gira0/subaru-floor-mat-retainer/preview/below-detail.png

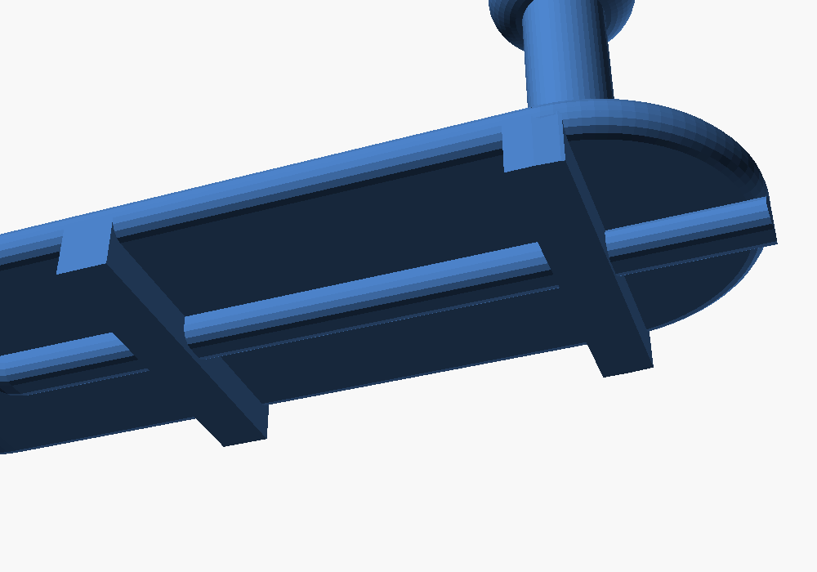
preview/below-detail.png
