gira0/subaru-floor-mat-retainer/preview/below.png

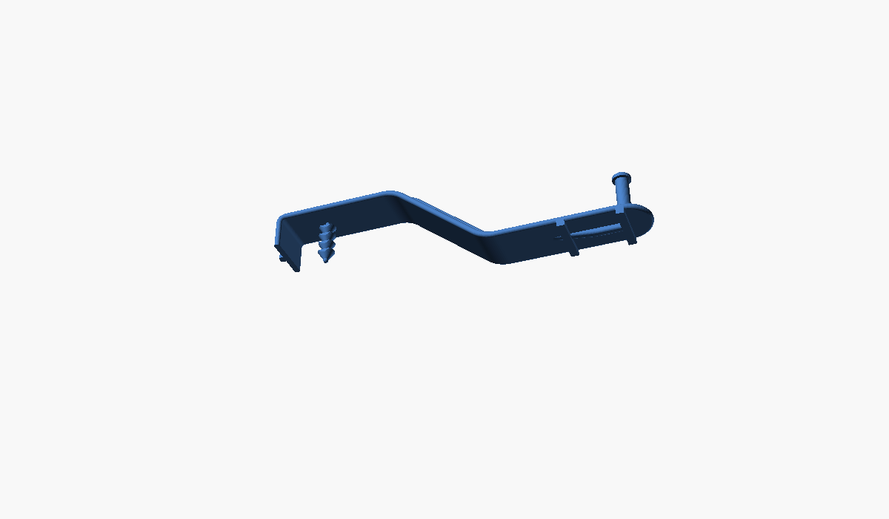
preview/below.png
