gira0/subaru-floor-mat-retainer/preview/clip-top.png

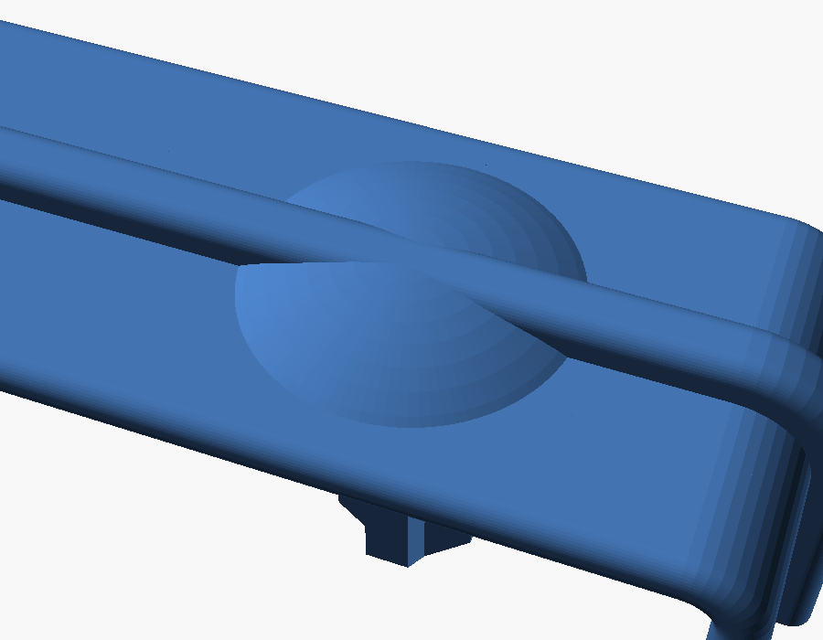
preview/clip-top.png
