gira0/subaru-floor-mat-retainer/preview/clip-varianten.png

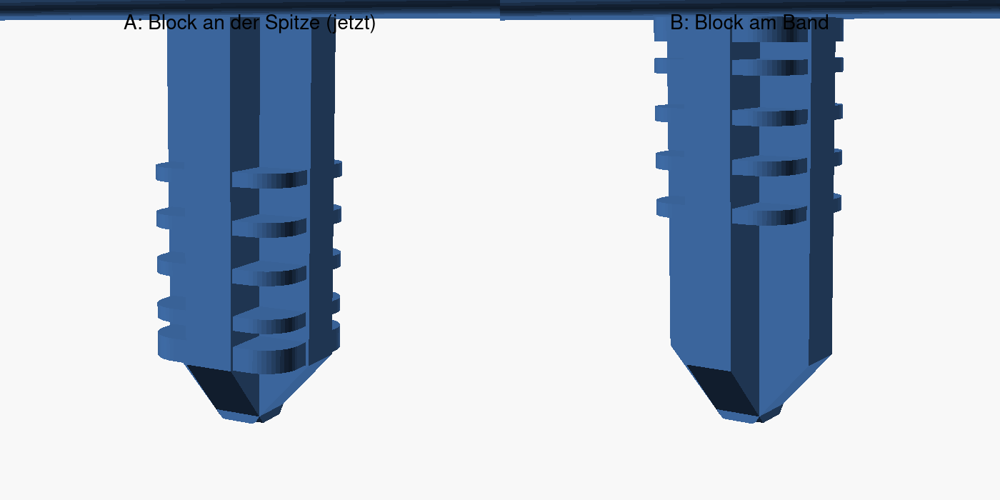
preview/clip-varianten.png
