gira0/subaru-floor-mat-retainer/preview/clip.png

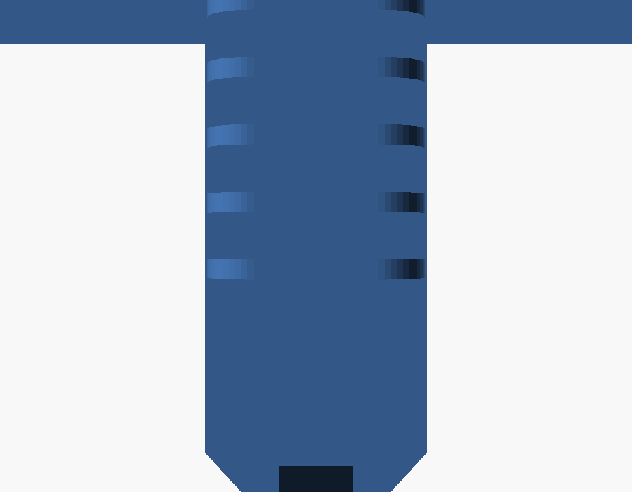
preview/clip.png
