gira0/subaru-floor-mat-retainer/preview/dimensions-check.png

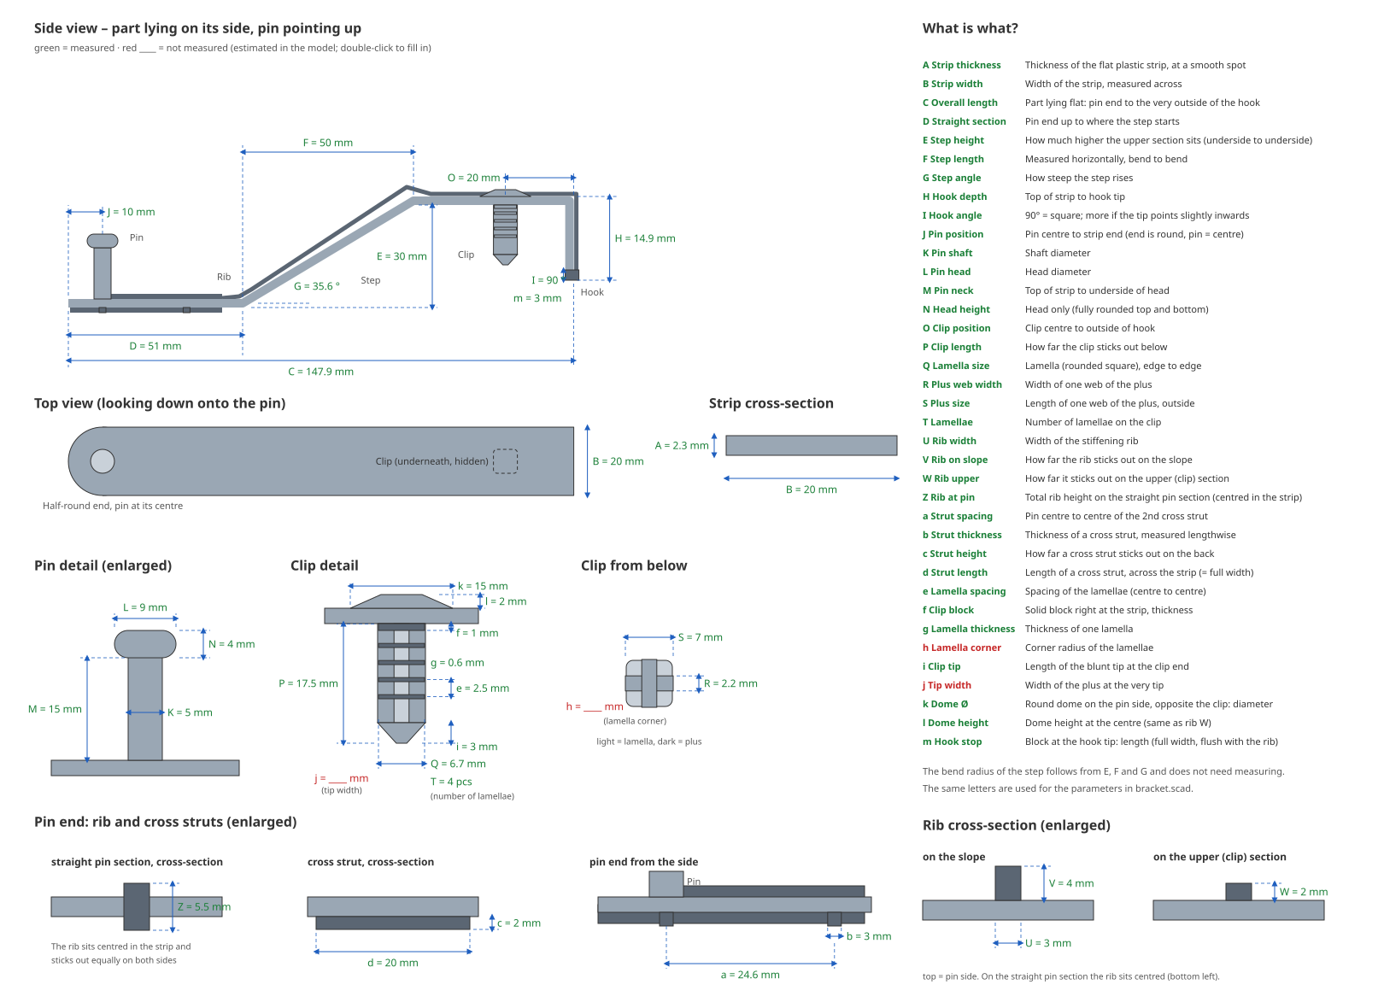
preview/dimensions-check.png
