gira0/subaru-floor-mat-retainer/preview/hook-stop2.png

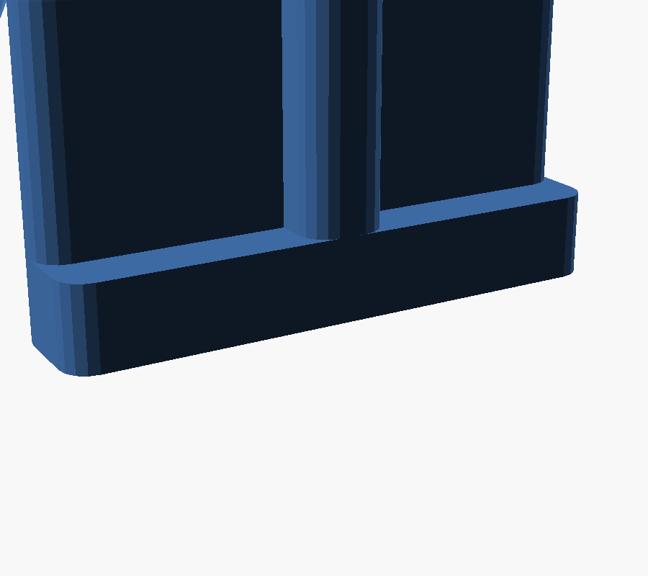
preview/hook-stop2.png
