gira0/subaru-floor-mat-retainer/preview/hook.png

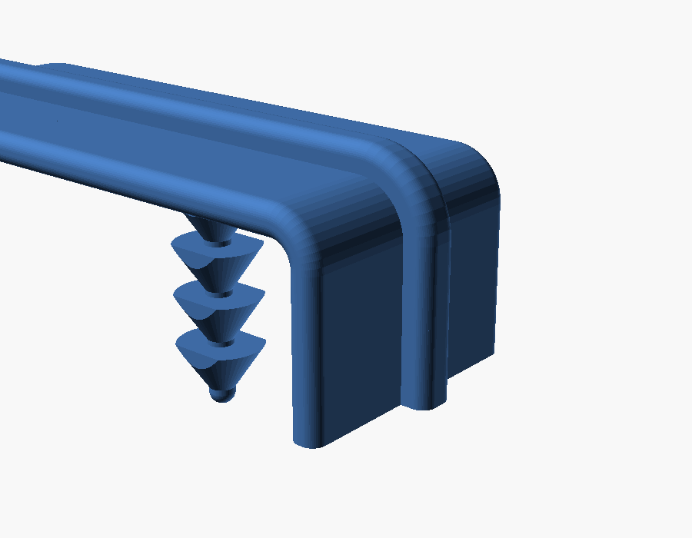
preview/hook.png
