gira0/subaru-floor-mat-retainer/preview/iso.png

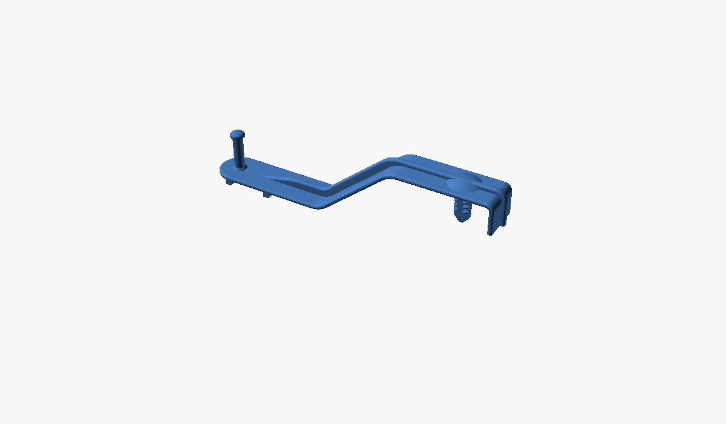
preview/iso.png
