gira0/subaru-floor-mat-retainer/preview/pin2.png

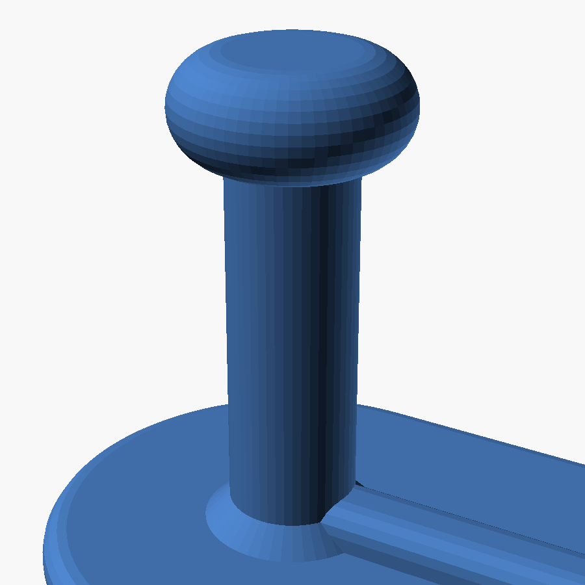
preview/pin2.png
