gira0/subaru-floor-mat-retainer/preview/pin-end-side.png

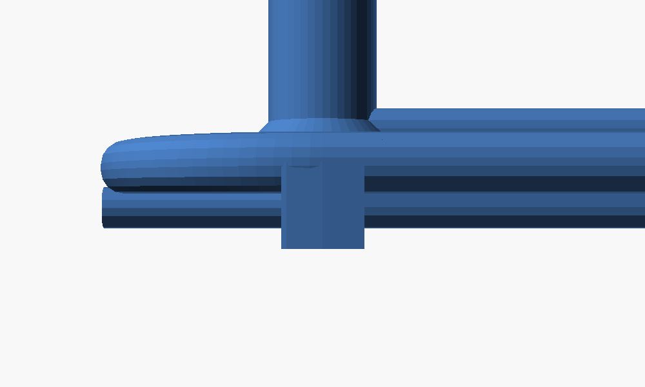
preview/pin-end-side.png
