gira0/subaru-floor-mat-retainer/preview/rib-bend1.png

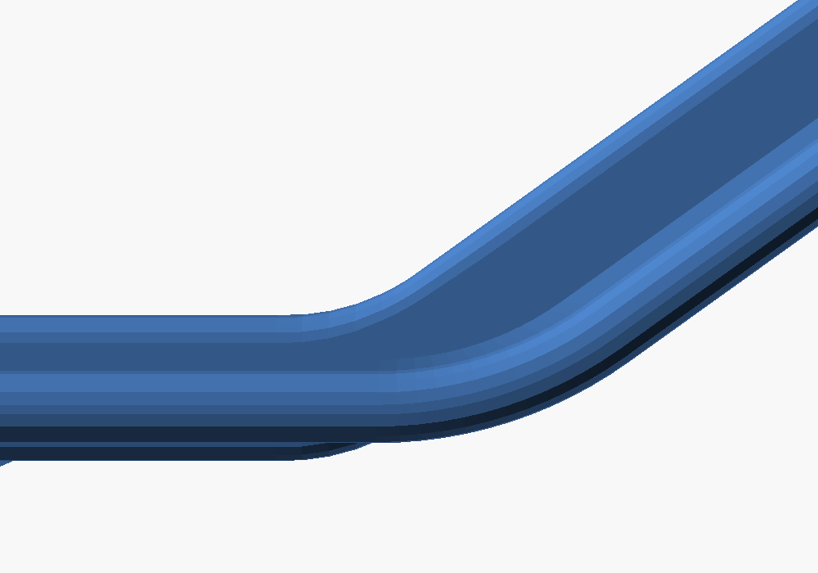
preview/rib-bend1.png
