gira0/subaru-floor-mat-retainer/preview/rib-bend1b.png

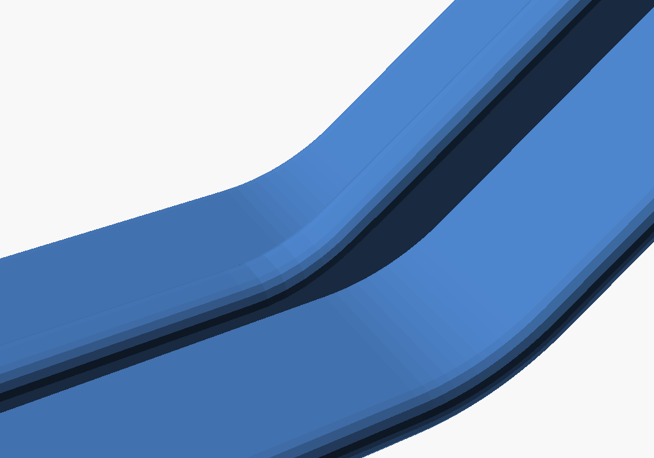
preview/rib-bend1b.png
