gira0/subaru-floor-mat-retainer/preview/rib-bend1c.png

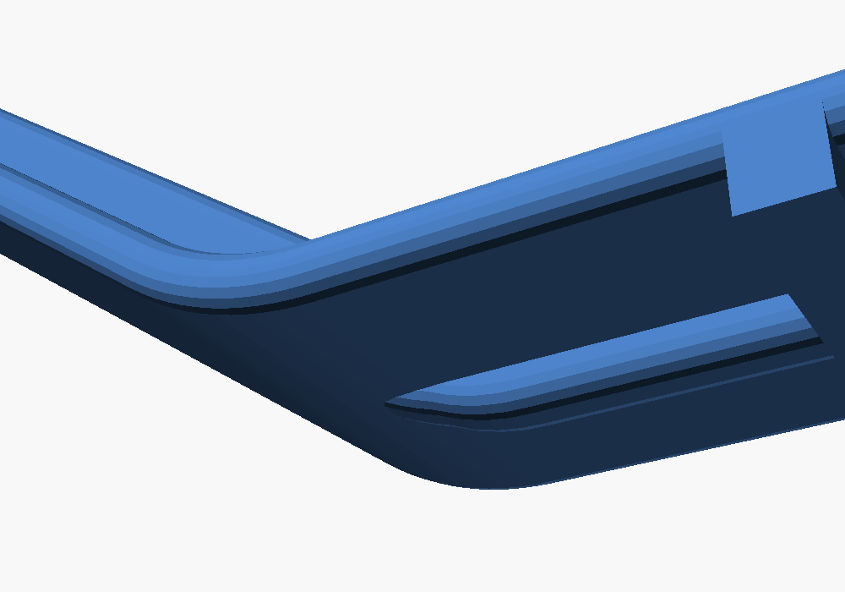
preview/rib-bend1c.png
