gira0/subaru-floor-mat-retainer/preview/rib-bend2.png

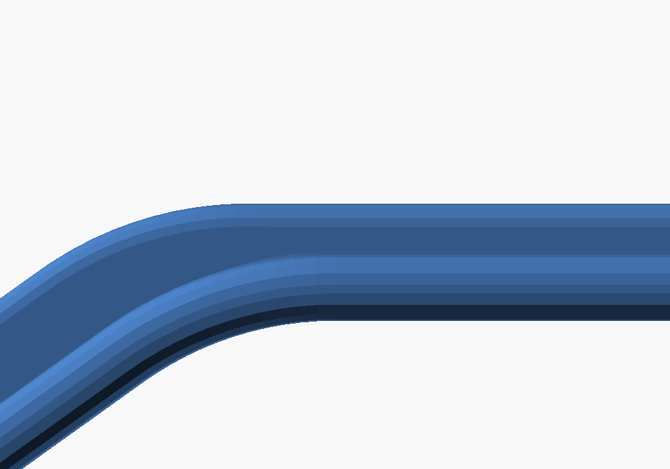
preview/rib-bend2.png
