gira0/subaru-floor-mat-retainer/preview/rib-bend2b.png

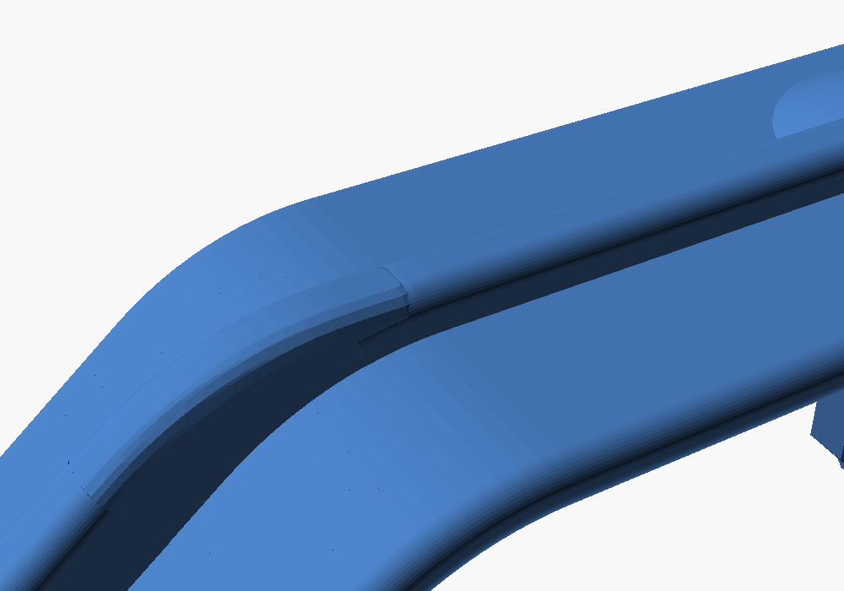
preview/rib-bend2b.png
