gira0/subaru-floor-mat-retainer/preview/rib-pin2.png

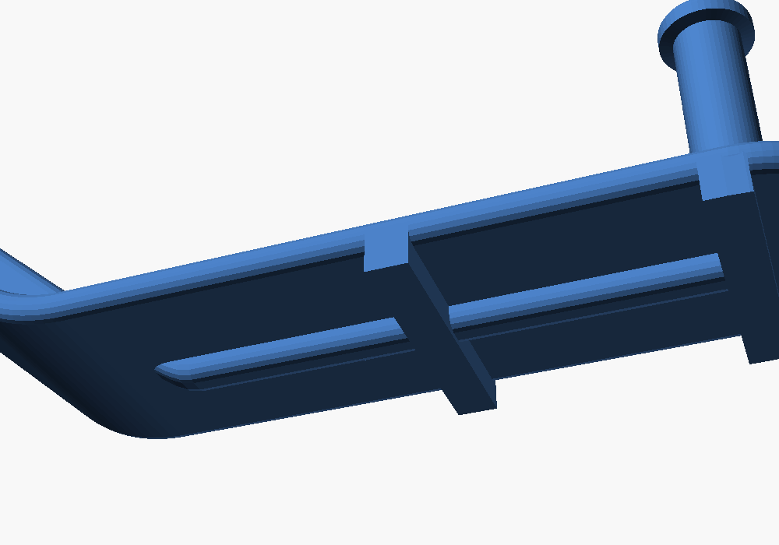
preview/rib-pin2.png
