gira0/subaru-floor-mat-retainer/preview/rib-pin.png

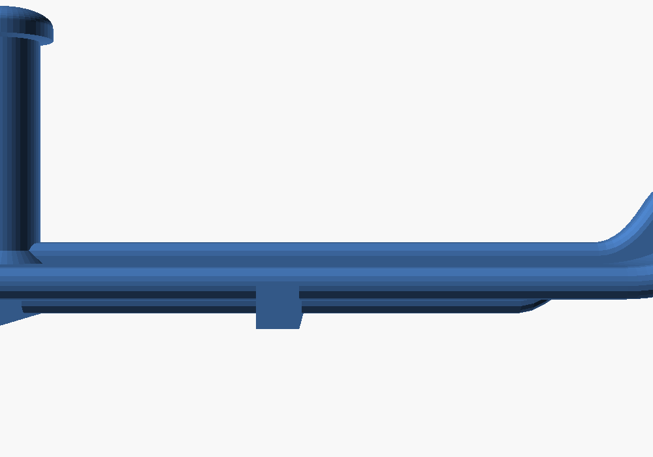
preview/rib-pin.png
