gira0/subaru-floor-mat-retainer/preview/side.png

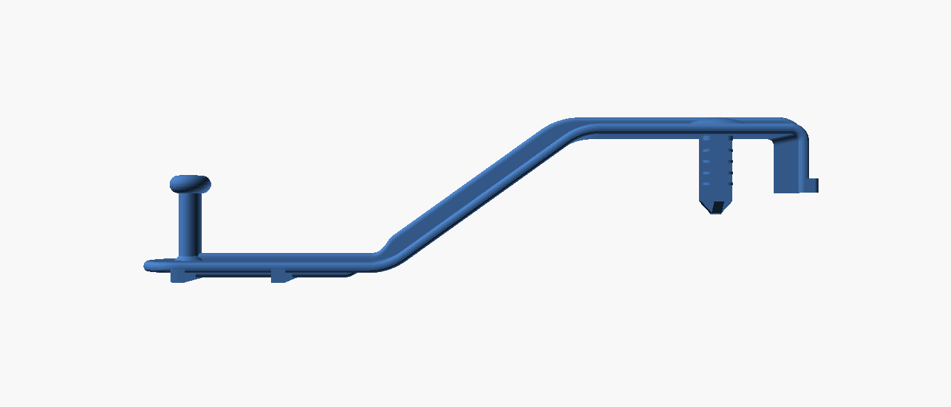
preview/side.png
