gira0/subaru-floor-mat-retainer/preview/top.png

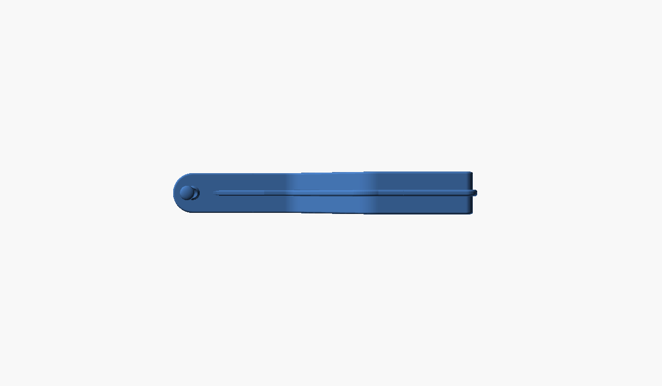
preview/top.png
