gira0/subaru-floor-mat-retainer/printables/02-side.png

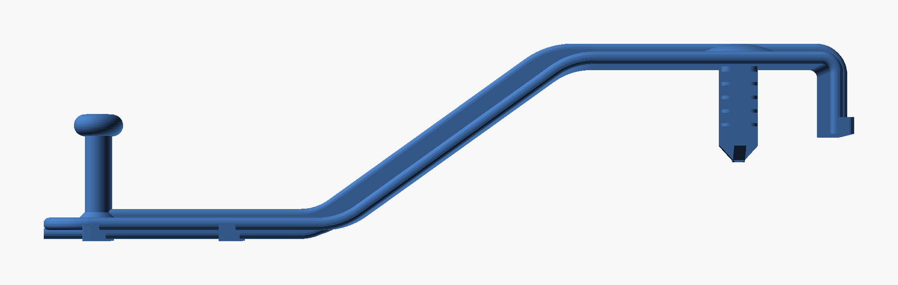
printables/02-side.png
