gira0/subaru-floor-mat-retainer/printables/03-below.png

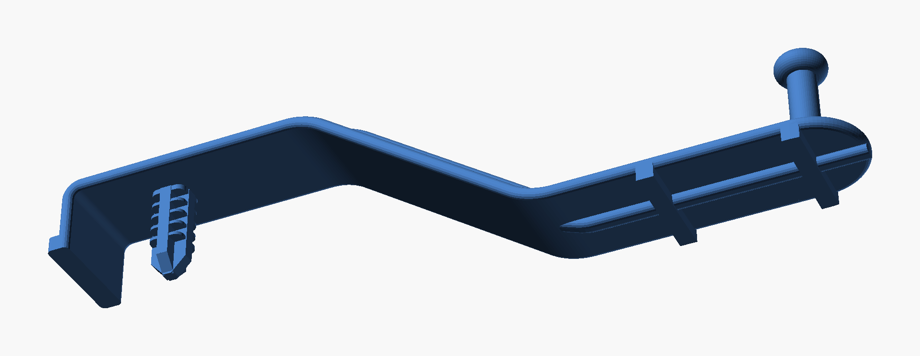
printables/03-below.png
