gira0/subaru-floor-mat-retainer/printables/04-clip-hook.png

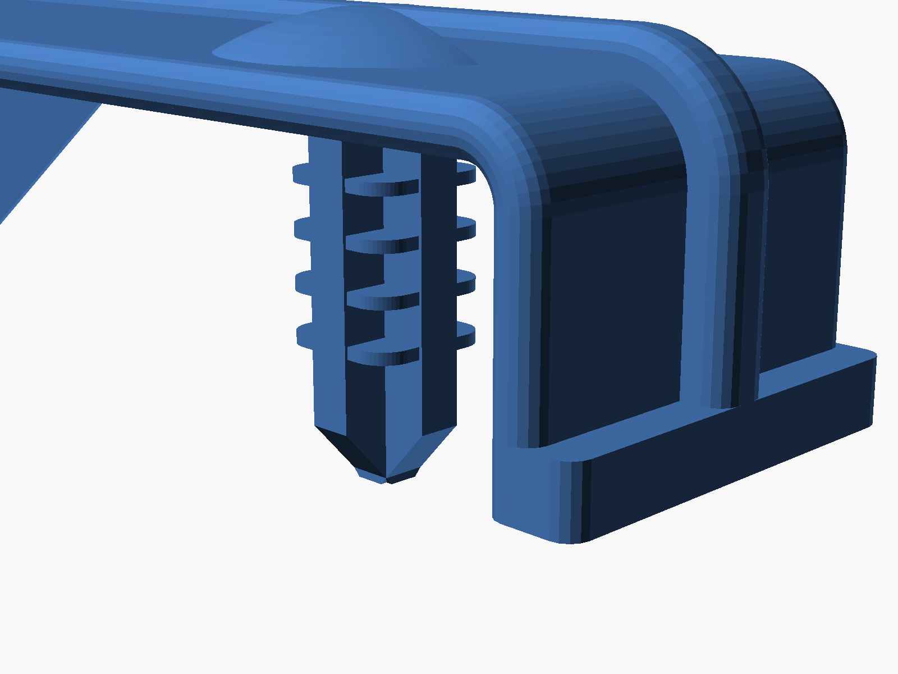
printables/04-clip-hook.png
