gira0/subaru-floor-mat-retainer/printables/05-pin-end.png

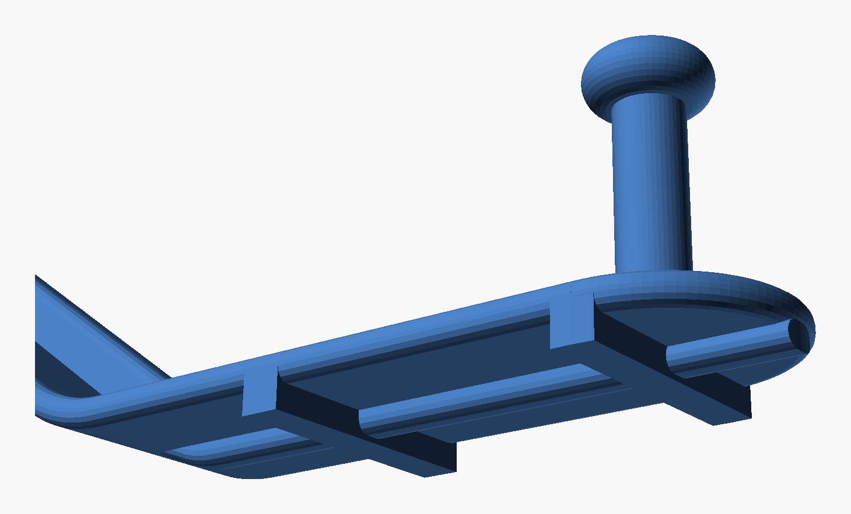
printables/05-pin-end.png
